wenzel-lab/SiPM-detector-module/images/sipm_output.png

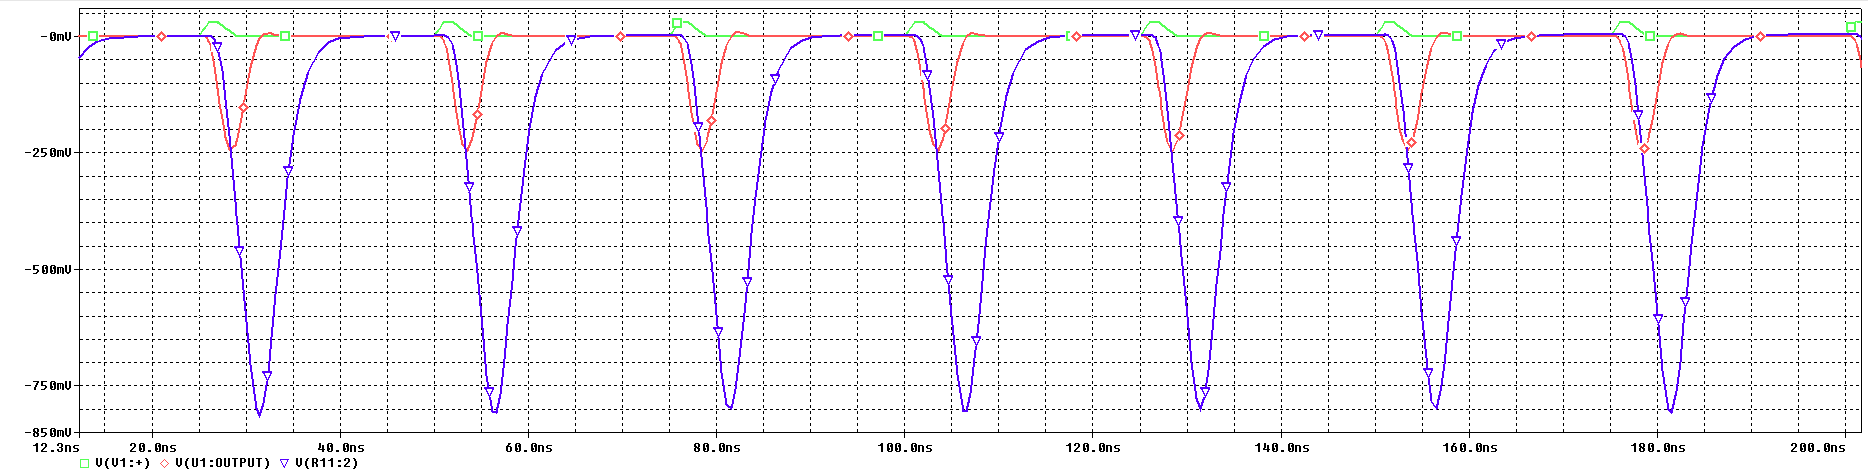
images/sipm_output.png
